Raduas/STM32-furnace/STM32-furnace/Core/Inc/base_funtions.h

/*
 * base_funtions.h
 *
 *  Created on: Aug 23, 2025
 *      Author: dolra
 */

#ifndef INC_BASE_FUNTIONS_H_
#define INC_BASE_FUNTIONS_H_

void allPWMStart(void);
void buckPWMStart(void);
void allPWMStop(void);
void buckPWMStop(void);


#endif /* INC_BASE_FUNTIONS_H_ */
